KaiserHK/Tesla-Turbine-Reconstruction/Tesla Turbine/Original Patent Design/Stator/STL/Original End Casting - FINAL.STL

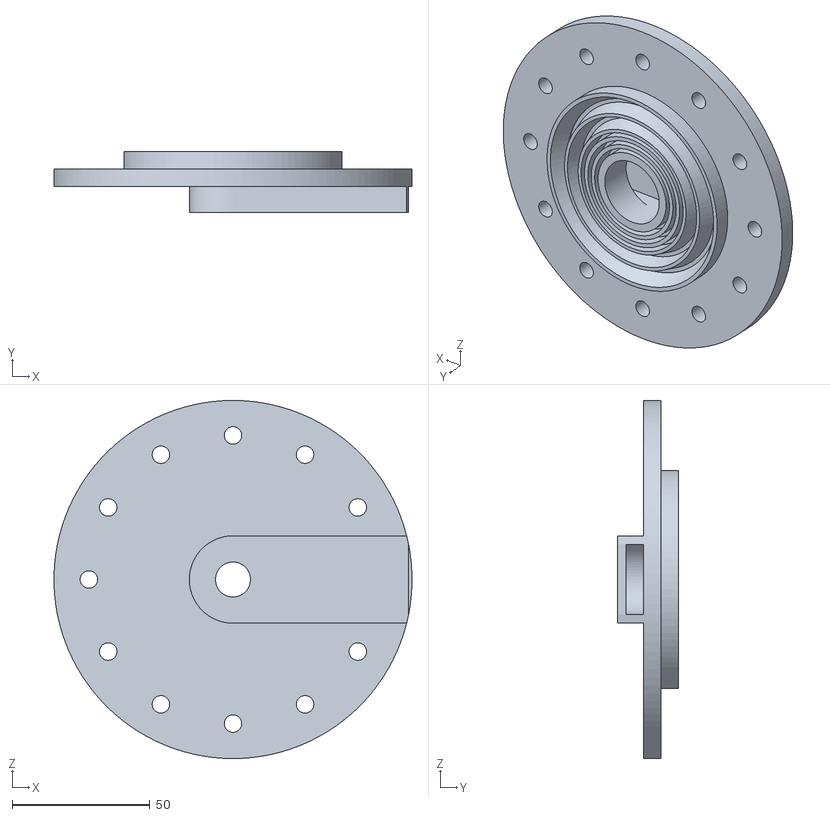
[picture p15: CAD file, 2023-10-09]
Tesla Turbine/Original Patent Design/Stator/STL/Original End Casting - FINAL.STL
130.1 x 22.2 x 130.2
