KaiserHK/Tesla-Turbine-Reconstruction/Tesla Turbine/Original Patent Design/Connecting Rods/SLDPRT/Outer Connecting Rod - FINAL.SLDPRT

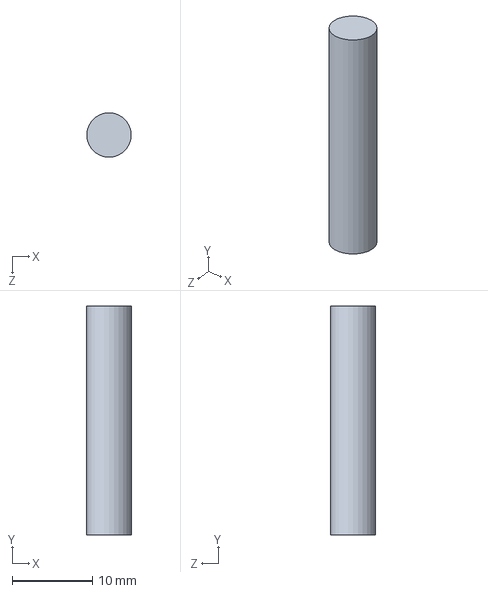
[picture p16: CAD file, 2023-10-09]
Tesla Turbine/Original Patent Design/Connecting Rods/SLDPRT/Outer Connecting Rod - FINAL.SLDPRT
5.56 x 28.6 x 5.56 mm
