KaiserHK/Tesla-Turbine-Reconstruction/Tesla Turbine/Original Patent Design/Stator/STL/Original End Casting.STL

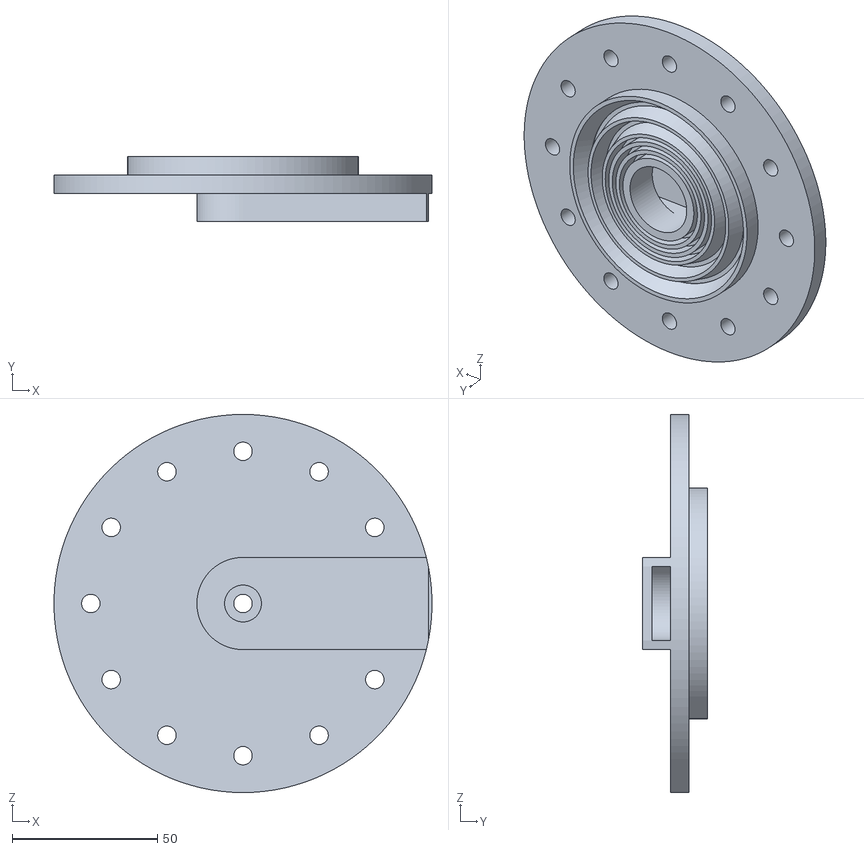
[picture p17: CAD file, 2023-10-09]
Tesla Turbine/Original Patent Design/Stator/STL/Original End Casting.STL
130.1 x 22.2 x 130.2
